quasiengineer/usb-pd-mch-hotplate/firmware/App/modules/display/display_font.c

#include "display_font.h"

const uint16_t Font8x16 [] = {
    0x0000,0x0000,0x0000,0x0000,0x0000,0x0000,0x0000,0x0000,0x0000,0x0000,0x0000,0x0000,0x0000,0x0000,0x0000,0x0000, //
    0x0000,0x0000,0x1800,0x1800,0x1800,0x1800,0x1800,0x1800,0x1800,0x0000,0x1800,0x1800,0x0000,0x0000,0x0000,0x0000, // !
    0x0000,0x6600,0x6600,0x6600,0x6600,0x0000,0x0000,0x0000,0x0000,0x0000,0x0000,0x0000,0x0000,0x0000,0x0000,0x0000, // "
    0x0000,0x0000,0x0000,0x6C00,0x6C00,0xFE00,0x6C00,0x6C00,0x6C00,0xFE00,0x6C00,0x6C00,0x0000,0x0000,0x0000,0x0000, // #
    0x1000,0x1000,0x7C00,0xD600,0xD200,0xD000,0x7C00,0x1600,0x1600,0x9600,0xD600,0x7C00,0x1000,0x1000,0x0000,0x0000, // $
    0x0000,0x0000,0x0000,0x0000,0xC200,0xC600,0x0C00,0x1800,0x3000,0x6000,0xC600,0x8600,0x0000,0x0000,0x0000,0x0000, // %
    0x0000,0x0000,0x3800,0x6C00,0x6C00,0x3800,0x7600,0xDC00,0xCC00,0xCC00,0xCC00,0x7600,0x0000,0x0000,0x0000,0x0000, // &
    0x0000,0x3000,0x3000,0x3000,0x6000,0x0000,0x0000,0x0000,0x0000,0x0000,0x0000,0x0000,0x0000,0x0000,0x0000,0x0000, // '
    0x0000,0x0000,0x0C00,0x1800,0x3000,0x3000,0x3000,0x3000,0x3000,0x3000,0x1800,0x0C00,0x0000,0x0000,0x0000,0x0000, // (
    0x0000,0x0000,0x3000,0x1800,0x0C00,0x0C00,0x0C00,0x0C00,0x0C00,0x0C00,0x1800,0x3000,0x0000,0x0000,0x0000,0x0000, // )
    0x0000,0x0000,0x0000,0x0000,0x0000,0x6600,0x3C00,0xFF00,0x3C00,0x6600,0x0000,0x0000,0x0000,0x0000,0x0000,0x0000, // *
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
    0x0000,0x0000,0xFE00,0xC000,0xC000,0xC000,0xF800,0xC000,0xC000,0xC000,0xC000,0xC000,0x0000,0x0000,0x0000,0x0000, // F
    0x0000,0x0000,0x7C00,0xC600,0xC000,0xC000,0xC000,0xDE00,0xC600,0xC600,0xC600,0x7A00,0x0000,0x0000,0x0000,0x0000, // G
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
};
