quasiengineer/usb-pd-mch-hotplate/firmware/App/modules/display/display_ssd1306.h

/**
 * This Library is written and optimized by Olivier Van den Eede(4ilo) in 2016
 * for Stm32 Uc and HAL-i2c lib's.
 *
 * To use this library with ssd1306 oled display you will need to customize the defines below.
 */

#ifndef _SSD1306_H
#define _SSD1306_H

#include "main.h"
#include "display_font.h"

// I2c address
#ifndef SSD1306_I2C_ADDR
#define SSD1306_I2C_ADDR        0x78
#endif // SSD1306_I2C_ADDR

// SSD1306 width in pixels
#ifndef SSD1306_WIDTH
#define SSD1306_WIDTH           128
#endif // SSD1306_WIDTH

// SSD1306 LCD height in pixels
#ifndef SSD1306_HEIGHT
#define SSD1306_HEIGHT          32
#endif // SSD1306_HEIGHT

#ifndef SSD1306_COM_LR_REMAP
#define SSD1306_COM_LR_REMAP    0
#endif // SSD1306_COM_LR_REMAP

#ifndef SSD1306_COM_ALTERNATIVE_PIN_CONFIG
#define SSD1306_COM_ALTERNATIVE_PIN_CONFIG    0
#endif // SSD1306_COM_ALTERNATIVE_PIN_CONFIG

//
//  Function definitions
//

uint8_t ssd1306_Init(I2C_HandleTypeDef *hi2c);
void ssd1306_UpdateScreen(I2C_HandleTypeDef *hi2c);
void ssd1306_Clear();
void ssd1306_PutString(const char * str, uint8_t charPosX, uint8_t charPosY, uint8_t fillEndWithSpaces);

#endif  // _SSD1306_H
